TheSlowGrowth/TapeLooper/dsp/src/dsp/TapeLooper.h

/**
 * Copyright (C) Johannes Elliesen, 2021
 *
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
 * You should have received a copy of the GNU General Public License
 * along with this program. If not, see <http://www.gnu.org/licenses/>.
 */

#pragma once

#include "DspHelpers.h"
#include "Player.h"
#include "Recorder.h"
#include "TapeProcessor.h"
#include "WowAndFlutter.h"

#include "../util/Memory.h"

template <size_t numChannels_>
struct LooperStoragePtr
{
    float* data[numChannels_];
    size_t numSamples;
    static constexpr size_t numChannels = numChannels_;

    size_t getTotalSizeInBytes() const
    {
        return numChannels * numSamples * sizeof(float);
    }
};

struct MonoOrStereoLooperStoragePtr :
    public LooperStoragePtr<1>,
    public LooperStoragePtr<2>
{
};

template <size_t size, size_t numChannels>
class LooperStorage : public LooperStoragePtr<numChannels>
{
public:
    LooperStorage()
    {
        for (size_t ch = 0; ch < numChannels; ch++)
        {
            storage_[ch].fill(0.0f);
            this->data[ch] = storage_[ch].data();
        }
        this->numSamples = size;
    }

private:
    std::array<std::array<float, size>, numChannels> storage_;
};

template <size_t sizeWhenMono>
class MonoOrStereoLooperStorage : public MonoOrStereoLooperStoragePtr
{
public:
    MonoOrStereoLooperStorage()
    {
        storage_.fill(0.0f);

        this->LooperStoragePtr<1>::data[0] = storage_.data();
        this->LooperStoragePtr<1>::numSamples = sizeWhenMono;

        const auto sizePerChannel = sizeWhenMono / 2;
        this->LooperStoragePtr<2>::data[0] = storage_.data();
        this->LooperStoragePtr<2>::data[1] = storage_.data() + sizePerChannel;
        this->LooperStoragePtr<2>::numSamples = sizePerChannel;
    }

private:
    std::array<float, sizeWhenMono> storage_;
};

enum class LooperState
{
    stopped,
    playing,
    recording
};

template <size_t sampleRate, size_t numChannels>
class TapeLooper
{
public:
    using ProcessorType = TapeProcessor<sampleRate, numChannels>;
    using SpeedModulatorType = WowAndFlutterOscillator<float, sampleRate>;
    using PlayerType = Player<ProcessorType, SpeedModulatorType, sampleRate, numChannels>;
    using RecorderType = Recorder<sampleRate, numChannels>;

    TapeLooper(LooperStoragePtr<numChannels> storageToUse) :
        storage_(storageToUse),
        state_(LooperState::stopped),
        player_(AudioBufferPtr<numChannels, const float>(storage_.data, storage_.numSamples)),
        recorder_(AudioBufferPtr<numChannels, float>(storage_.data, storage_.numSamples))
    {
    }

    void switchState(LooperState newState)
    {
        switch (newState)
        {
            default:
            case LooperState::stopped:
                if (state_ == LooperState::recording)
                    recorder_.stopRecording();
                else if (state_ == LooperState::playing)
                    player_.stopPlaying();
                break;
            case LooperState::playing:
                if (preventPlayback_)
                    return;
                if (state_ == LooperState::recording)
                    recorder_.stopRecording();
                player_.startPlaying(recorder_.getCurrentRecordingLength());
                break;
            case LooperState::recording:
                if (preventRecording_)
                    return;
                if (state_ == LooperState::playing)
                    player_.stopPlaying();
                recorder_.startRecording();
                break;
        }
        state_ = newState;
    }

    bool isRecording() const { return recorder_.isRecording(); }

    LooperState getState() const { return state_; }

    void reset()
    {
        player_.reset();
        recorder_.reset();
    }

    void process(float paramSpeed,
                 float wowAndFlutterAmt,
                 Direction direction,
                 const typename ProcessorType::Parameters& processorParameters,
                 float paramPostGain,
                 AudioBufferPtr<numChannels, const float> input,
                 AudioBufferPtr<numChannels, float> outputToAddTo,
                 ExponentialSmoother::TimeConstant postGainSmootherTimeConstant =
                     ExponentialSmoother::TimeConstant(0.05f, sampleRate, 1),
                 ExponentialSmoother::TimeConstant speedSmootherTimeConstant =
                     ExponentialSmoother::TimeConstant(0.05f, sampleRate, 1))
    {
        const auto mappedWowAndFlutterAmt = wowAndFlutterAmt * wowAndFlutterAmt;
        player_.process(paramSpeed,
                        mappedWowAndFlutterAmt,
                        direction,
                        paramPostGain,
                        processorParameters,
                        outputToAddTo,
                        postGainSmootherTimeConstant,
                        speedSmootherTimeConstant);
        recorder_.process(input);

        const auto recordingStopped = state_ == LooperState::recording && !recorder_.isRecording();
        if (recordingStopped)
            switchState(LooperState::playing);
    }

    size_t getSaveAndRecallStorageSize() const
    {
        return recorder_.getSaveAndRecallStorageSize()
               + sizeof(uint8_t) // isPlaying?
               + storage_.getTotalSizeInBytes();
    }

    /**
     * Saves the state of the looper
     */
    template <typename StorageType>
    bool save(WritableMemory<StorageType>& mem) const
    {
        if (!recorder_.save(mem))
            return false;

        // write sample data
        for (size_t ch = 0; ch < numChannels; ch++)
        {
            if (!mem.writeRaw(storage_.data[ch], sizeof(float) * storage_.numSamples))
                return false;
        }

        const uint8_t isPlaying = state_ == LooperState::playing ? 1 : 0;

        return mem.writeItems(isPlaying);
    }

    /**
     * Stopps playback or recording and recalls the state of the looper, including
     *    - the length of the current recording
     *    - if the looper is currently playing
     *    - the sample data stored
     */
    template <typename StorageType>
    bool restore(ReadableMemory<StorageType>& mem)
    {
        if (preventRecording_)
            return false;
        if (!recorder_.restore(mem))
            return false;

        // read sample data
        for (size_t ch = 0; ch < numChannels; ch++)
        {
            if (!mem.readRaw(storage_.data[ch], sizeof(float) * storage_.numSamples))
                return false;
        }

        uint8_t isPlaying = 0;
        mem.readItems(isPlaying);

        switchState(isPlaying == 1 ? LooperState::playing : LooperState::stopped);
        return true;
    }

    void preventPlaybackAndRecording(bool stopRecordingImmediately = false)
    {
        preventPlayback_ = true;
        preventRecording_ = true;
        const auto previousState = getState();
        switchState(LooperState::stopped);
        if (previousState == LooperState::recording)
        {
            if (stopRecordingImmediately)
                recorder_.stopRecordingImmediately();
        }
    }

    void preventRecording(bool stopRecordingImmediately = false)
    {
        preventPlayback_ = false;
        preventRecording_ = true;

        if (getState() == LooperState::recording)
        {
            switchState(LooperState::stopped);
            if (stopRecordingImmediately)
                recorder_.stopRecordingImmediately();
        }
    }

    void liftRestrictions()
    {
        preventPlayback_ = false;
        preventRecording_ = false;
    }

    LooperStoragePtr<numChannels> getSampleStoragePtr() { return storage_; }
    void setPlaybackLength(size_t length) { recorder_.setCurrentPlaybackLength(length); }
    size_t getPlaybackLength() const { return recorder_.getCurrentRecordingLength(); }
    static constexpr size_t getNumChannels() { return numChannels; }
    static constexpr size_t getSampleRate() { return sampleRate; }

    RecorderType& recorderForTesting() { return recorder_; }

private:
    const LooperStoragePtr<numChannels> storage_;
    LooperState state_;
    PlayerType player_;
    RecorderType recorder_;
    bool preventPlayback_ = false;
    bool preventRecording_ = false;
};
