TheSlowGrowth/TapeLooper/dsp/src/dsp/DspHelpers.cpp

#include "DspHelpers.h"

/* original script taken from pichenettes/stmlib */
const float pitchRatioHigh[257] = {
    // clang-format off
    6.151958251e-04,  6.517772725e-04,  6.905339660e-04,  7.315952524e-04,
    7.750981699e-04,  8.211879055e-04,  8.700182794e-04,  9.217522585e-04,
    9.765625000e-04,  1.034631928e-03,  1.096154344e-03,  1.161335073e-03,
    1.230391650e-03,  1.303554545e-03,  1.381067932e-03,  1.463190505e-03,
    1.550196340e-03,  1.642375811e-03,  1.740036559e-03,  1.843504517e-03,
    1.953125000e-03,  2.069263856e-03,  2.192308688e-03,  2.322670146e-03,
    2.460783301e-03,  2.607109090e-03,  2.762135864e-03,  2.926381010e-03,
    3.100392680e-03,  3.284751622e-03,  3.480073118e-03,  3.687009034e-03,
    3.906250000e-03,  4.138527712e-03,  4.384617376e-03,  4.645340293e-03,
    4.921566601e-03,  5.214218180e-03,  5.524271728e-03,  5.852762019e-03,
    6.200785359e-03,  6.569503244e-03,  6.960146235e-03,  7.374018068e-03,
    7.812500000e-03,  8.277055425e-03,  8.769234752e-03,  9.290680586e-03,
    9.843133202e-03,  1.042843636e-02,  1.104854346e-02,  1.170552404e-02,
    1.240157072e-02,  1.313900649e-02,  1.392029247e-02,  1.474803614e-02,
    1.562500000e-02,  1.655411085e-02,  1.753846950e-02,  1.858136117e-02,
    1.968626640e-02,  2.085687272e-02,  2.209708691e-02,  2.341104808e-02,
    2.480314144e-02,  2.627801298e-02,  2.784058494e-02,  2.949607227e-02,
    3.125000000e-02,  3.310822170e-02,  3.507693901e-02,  3.716272234e-02,
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
    1.030231638e+00,  1.030464119e+00,  1.030696653e+00,  1.030929239e+00,
    1.031161878e+00,  1.031394569e+00,  1.031627313e+00,  1.031860109e+00,
    1.032092958e+00,  1.032325859e+00,  1.032558813e+00,  1.032791820e+00,
    1.033024879e+00,  1.033257991e+00,  1.033491155e+00,  1.033724372e+00,
    1.033957641e+00,  1.034190964e+00,  1.034424338e+00,  1.034657766e+00,
    1.034891246e+00,  1.035124779e+00,  1.035358364e+00,  1.035592003e+00,
    1.035825694e+00,  1.036059437e+00,  1.036293234e+00,  1.036527083e+00,
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
    // clang-format on
};
