TheSlowGrowth/TapeLooper/dsp/src/dsp/AudioBuffer.h

/**
 * Copyright (C) Johannes Elliesen, 2021
 *
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
 * You should have received a copy of the GNU General Public License
 * along with this program. If not, see <http://www.gnu.org/licenses/>.
 */

#pragma once

#include <array>

template <size_t numChannels, typename FloatType = float>
class AudioBufferPtr
{
public:
    AudioBufferPtr(FloatType* const* buffer, size_t numSamplesPerChannel) :
        size_(numSamplesPerChannel)
    {
        for (size_t ch = 0; ch < numChannels; ch++)
            buffer_[ch] = buffer[ch];
    }

    AudioBufferPtr(const AudioBufferPtr& other) = default;

    FloatType* operator[](size_t channelIdx)
    {
        return buffer_[channelIdx];
    }

    const FloatType* operator[](size_t channelIdx) const
    {
        return buffer_[channelIdx];
    }

    FloatType* const* getChannelPointers()
    {
        return buffer_;
    }

    const FloatType* const* getChannelPointers() const
    {
        return buffer_;
    }

    operator AudioBufferPtr<numChannels, const FloatType>() const
    {
        return AudioBufferPtr<numChannels, const FloatType>(buffer_, size_);
    }

    void fill(FloatType value)
    {
        for (size_t ch = 0; ch < numChannels; ch++)
            for (size_t i = 0; i < size_; i++)
                buffer_[ch][i] = value;
    }

    void copyToChannel(size_t destChannel, const FloatType* const srcSamples, size_t numSamples)
    {
        for (size_t i = 0; i < std::min(numSamples, size_); i++)
            buffer_[destChannel][i] = srcSamples[i];
    }

    void addToChannel(size_t destChannel, const FloatType* const srcSamples, size_t numSamples)
    {
        for (size_t i = 0; i < std::min(numSamples, size_); i++)
            buffer_[destChannel][i] += srcSamples[i];
    }

    void applyGain(FloatType value)
    {
        for (size_t ch = 0; ch < numChannels; ch++)
            for (size_t i = 0; i < size_; i++)
                buffer_[ch][i] *= value;
    }

    AudioBufferPtr<numChannels, FloatType> subBlock(size_t startSample, size_t length = size_t(-1)) const
    {
        const auto resultMaxLength = std::max(size_ - startSample, size_t(0));
        const auto resultLength = std::min(resultMaxLength, length);
        AudioBufferPtr<numChannels, FloatType> result(resultLength);
        for (size_t ch = 0; ch < numChannels; ch++)
            result.buffer_[ch] = buffer_[ch] + startSample;
        return result;
    }

    const size_t size_;

protected:
    // private ctor for use in subBlock()
    AudioBufferPtr(size_t numSamples) :
        size_(numSamples) {}

    FloatType* buffer_[numChannels];
};

template <size_t numChannels, size_t numSamples, typename FloatType = float>
class AudioBuffer : public AudioBufferPtr<numChannels, FloatType>
{
public:
    AudioBuffer() :
        AudioBufferPtr<numChannels, FloatType>(numSamples)
    {
        for (size_t ch = 0; ch < numChannels; ch++)
            this->buffer_[ch] = channelBuffers_[ch];
    }

private:
    std::array<FloatType[numSamples], numChannels> channelBuffers_;
};
