TheSlowGrowth/TapeLooper/firmware/src/ui/UiSettingsPage.h

/**
 * Copyright (C) Johannes Elliesen, 2021
 *
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
 * You should have received a copy of the GNU General Public License
 * along with this program. If not, see <http://www.gnu.org/licenses/>.
 */

#pragma once

#include <array>
#include <memory>

#include <ui/UI.h>
#include <dsp/TapeLooper.h>

#include "../constants.h"
#include "../LooperController.h"
#include "../hardware/UiHardwareTypes.h"
#include "LooperParameterProvider.h"

template <typename LooperControllerType, typename UiHardwareType, typename LooperParameterProviderType>
class UiSettingsPage : public daisy::UiPage
{
public:
    UiSettingsPage(LooperControllerType& looperController,
                   LooperParameterProviderType& looperParameterProvider,
                   daisy::UiPage& calibrationPage) :
        looperController_(looperController),
        looperParameterProvider_(looperParameterProvider),
        calibrationPage_(calibrationPage)
    {
    }

    virtual ~UiSettingsPage() {}

    bool IsOpaque(const daisy::UiCanvasDescriptor&) override { return false; }

    void Draw(const daisy::UiCanvasDescriptor& canvas) override
    {
        UiHardwareType& hardware = *((UiHardwareType*) canvas.handle_);

        // light up the settings page led
        if (currentSetting_ == Setting::direction)
            hardware.setLed(Led::settings, LedColour::pulsingRed);
        else if (currentSetting_ == Setting::numChannels)
            hardware.setLed(Led::settings, LedColour::pulsingYellow);
        else
            hardware.setLed(Led::settings, LedColour::pulsingGreen);

        // update channel octave LEDs to show the currently selected setting
        const auto updateChannelOctaveLeds = [&](size_t looperChannel, std::array<Led, 4> ledIds)
        {
            if (currentSetting_ == Setting::direction)
            {
                if (looperController_.getDirection(looperChannel) == Direction::forwards)
                {
                    hardware.setLed(ledIds[0], LedColour::off);
                    hardware.setLed(ledIds[1], LedColour::off);
                    hardware.setLed(ledIds[2], LedColour::red);
                    hardware.setLed(ledIds[3], LedColour::red);
                }
                else
                {
                    hardware.setLed(ledIds[0], LedColour::red);
                    hardware.setLed(ledIds[1], LedColour::red);
                    hardware.setLed(ledIds[2], LedColour::off);
                    hardware.setLed(ledIds[3], LedColour::off);
                }
            }
            else if (currentSetting_ == Setting::numChannels)
            {
                hardware.setLed(ledIds[0], LedColour::yellow);
                hardware.setLed(ledIds[1], LedColour::yellow);
                if (looperController_.getChannelLayout(looperChannel) == ChannelLayout::stereo)
                {
                    hardware.setLed(ledIds[2], LedColour::yellow);
                    hardware.setLed(ledIds[3], LedColour::yellow);
                }
                else
                {
                    hardware.setLed(ledIds[2], LedColour::off);
                    hardware.setLed(ledIds[3], LedColour::off);
                }
            }
            else
            {
                const auto acceleration = looperController_.getMotorAcceleration(looperChannel);
                hardware.setLed(ledIds[0],
                                acceleration == MotorAcceleration::verySlow
                                    ? LedColour::green
                                    : LedColour::off);
                hardware.setLed(ledIds[1],
                                (acceleration == MotorAcceleration::slow) || (acceleration == MotorAcceleration::medium)
                                    ? LedColour::green
                                    : LedColour::off);
                hardware.setLed(ledIds[2],
                                (acceleration == MotorAcceleration::medium) || (acceleration == MotorAcceleration::fast)
                                    ? LedColour::green
                                    : LedColour::off);
                hardware.setLed(ledIds[3],
                                acceleration == MotorAcceleration::veryFast
                                    ? LedColour::green
                                    : LedColour::off);
            }
        };
        updateChannelOctaveLeds(0, { Led::chA_m2, Led::chA_m1, Led::chA_p1, Led::chA_p2 });
        updateChannelOctaveLeds(1, { Led::chB_m2, Led::chB_m1, Led::chB_p1, Led::chB_p2 });
        updateChannelOctaveLeds(2, { Led::chC_m2, Led::chC_m1, Led::chC_p1, Led::chC_p2 });
        updateChannelOctaveLeds(3, { Led::chD_m2, Led::chD_m1, Led::chD_p1, Led::chD_p2 });
    }

    void OnFocusGained() override
    {
        currentSetting_ = Setting::direction;
        saveButtonState_ = false;
        loadButtonState_ = false;
    }

    bool OnButton(uint16_t buttonID, uint8_t numberOfPresses, bool isRetriggering) override
    {
        (void) (isRetriggering); // ignore this argument

        const Button button = Button(buttonID);

        trackLoadAndSaveButtonStates(button, numberOfPresses);

        // swallow but ignore button-up messages
        if (numberOfPresses < 1)
            return true;

        switch (button)
        {
            // channel up rocker switch
            case Button::chA_up:
                onUpButton(0);
                break;
            case Button::chB_up:
                onUpButton(1);
                break;
            case Button::chC_up:
                onUpButton(2);
                break;
            case Button::chD_up:
                onUpButton(3);
                break;
            // channel down rocker switch
            case Button::chA_down:
                onDownButton(0);
                break;
            case Button::chB_down:
                onDownButton(1);
                break;
            case Button::chC_down:
                onDownButton(2);
                break;
            case Button::chD_down:
                onDownButton(3);
                break;
            // cycle through settings; then return to base page
            case Button::settings:
                if (currentSetting_ == Setting::direction)
                    currentSetting_ = Setting::numChannels;
                else if (currentSetting_ == Setting::numChannels)
                    currentSetting_ = Setting::motorLag;
                else if (currentSetting_ == Setting::motorLag)
                    Close(); // close this page
                break;

            // open calibration menu when load and save pressed at the same time
            case Button::load:
            case Button::save:
                if (saveButtonState_ && loadButtonState_)
                {
                    auto* parent = GetParentUI();
                    Close();
                    parent->OpenPage(calibrationPage_);
                }
            default:
                break;
        }
        return true;
    }

    bool OnPotMoved(uint16_t, float) override
    {
        return false; // passthrough pot events to the base page
    }

private:
    UiSettingsPage(const UiSettingsPage&) = delete;
    UiSettingsPage& operator=(const UiSettingsPage&) = delete;

    void trackLoadAndSaveButtonStates(Button button, int numberOfPresses)
    {
        if (button == Button::save)
        {
            saveButtonState_ = numberOfPresses > 0;
        }
        if (button == Button::load)
        {
            loadButtonState_ = numberOfPresses > 0;
        }
    }

    void onUpButton(size_t looperChannel)
    {
        if (currentSetting_ == Setting::direction)
        {
            if (looperController_.getDirection(looperChannel) != Direction::forwards)
                looperController_.setDirection(looperChannel, Direction::forwards);
        }
        else if (currentSetting_ == Setting::numChannels)
        {
            if (looperController_.getChannelLayout(looperChannel) != ChannelLayout::stereo)
                looperController_.setChannelLayout(looperChannel, ChannelLayout::stereo);
        }
        else
        {
            auto currentAcceleration = looperController_.getMotorAcceleration(looperChannel);
            switch (currentAcceleration)
            {
                case MotorAcceleration::verySlow:
                    looperController_.setMotorAcceleration(looperChannel, MotorAcceleration::slow);
                    break;
                case MotorAcceleration::slow:
                    looperController_.setMotorAcceleration(looperChannel, MotorAcceleration::medium);
                    break;
                case MotorAcceleration::medium:
                    looperController_.setMotorAcceleration(looperChannel, MotorAcceleration::fast);
                    break;
                case MotorAcceleration::fast:
                    looperController_.setMotorAcceleration(looperChannel, MotorAcceleration::veryFast);
                    break;
                default:
                    break;
            }
        }
    }

    void onDownButton(size_t looperChannel)
    {
        if (currentSetting_ == Setting::direction)
        {
            if (looperController_.getDirection(looperChannel) != Direction::backwards)
                looperController_.setDirection(looperChannel, Direction::backwards);
        }
        else if (currentSetting_ == Setting::numChannels)
        {
            if (looperController_.getChannelLayout(looperChannel) != ChannelLayout::mono)
                looperController_.setChannelLayout(looperChannel, ChannelLayout::mono);
        }
        else
        {
            auto currentAcceleration = looperController_.getMotorAcceleration(looperChannel);
            switch (currentAcceleration)
            {
                case MotorAcceleration::veryFast:
                    looperController_.setMotorAcceleration(looperChannel, MotorAcceleration::fast);
                    break;
                case MotorAcceleration::fast:
                    looperController_.setMotorAcceleration(looperChannel, MotorAcceleration::medium);
                    break;
                case MotorAcceleration::medium:
                    looperController_.setMotorAcceleration(looperChannel, MotorAcceleration::slow);
                    break;
                case MotorAcceleration::slow:
                    looperController_.setMotorAcceleration(looperChannel, MotorAcceleration::verySlow);
                    break;
                default:
                    break;
            }
        }
    }

    enum class Setting
    {
        direction,
        numChannels,
        motorLag
    };
    Setting currentSetting_ = Setting::direction;

    bool saveButtonState_ = false;
    bool loadButtonState_ = false;

    LooperControllerType& looperController_;
    LooperParameterProviderType& looperParameterProvider_;

    daisy::UiPage& calibrationPage_;
};
