TheSlowGrowth/TapeLooper/firmware/src/ui/TapeLooperUi.h

/**
 * Copyright (C) Johannes Elliesen, 2021
 *
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
 * You should have received a copy of the GNU General Public License
 * along with this program. If not, see <http://www.gnu.org/licenses/>.
 */

#pragma once

#include <array>

#include <ui/UI.h>
#include <dsp/DspHelpers.h>

#include "LooperParameterProvider.h"
#include "UiBasePage.h"
#include "UiCalibrationPage.h"
#include "UiSettingsPage.h"
#include "UiLoadOrSavePage.h"
#include "UiRecordingPage.h"

template <typename UiHardwareType,
          typename PeakMeterType,
          typename LooperControllerType,
          typename ParameterProviderType,
          typename LoopLibraryType>
class TapeLooperUi
{
public:
    TapeLooperUi(UiHardwareType& uiHardware,
                 daisy::UiCanvasDescriptor::ClearFuncPtr clearFunction,
                 daisy::UiCanvasDescriptor::FlushFuncPtr flushFunction,
                 daisy::UiEventQueue& eventQueue,
                 const std::array<PeakMeterType, 4>& peakMeters,
                 LooperControllerType& looperController,
                 ParameterProviderType& looperParameterProvider,
                 LoopLibraryType& loopLibrary) :
        uiHardware_(uiHardware),
        eventQueue_(eventQueue),
        calibrationPage_(uiHardware),
        settingsPage_(looperController,
                      looperParameterProvider,
                      calibrationPage_),
        savePage_(looperController, loopLibrary),
        loadPage_(looperController, loopLibrary),
        recordingPage_(looperController),
        basePage_(peakMeters,
                  looperController,
                  looperParameterProvider,
                  settingsPage_,
                  savePage_,
                  loadPage_,
                  recordingPage_)
    {
        daisy::UiCanvasDescriptor ledCanvas;
        ledCanvas.clearFunction_ = clearFunction;
        ledCanvas.flushFunction_ = flushFunction;
        ledCanvas.handle_ = &uiHardware_;
        ledCanvas.id_ = 0;
        ledCanvas.updateRateMs_ = 20; // 50Hz

        ui_.Init(eventQueue_,
                 daisy::UI::SpecialControlIds {},
                 { ledCanvas });
        ui_.OpenPage(basePage_);
    }

    void process()
    {
        ui_.Process();
    }

private:
    TapeLooperUi(const TapeLooperUi&) = delete;
    TapeLooperUi& operator=(const TapeLooperUi&) = delete;

    UiHardwareType& uiHardware_;
    daisy::UiEventQueue& eventQueue_;
    daisy::UI ui_;
    UiCalibrationPage<UiHardwareType>
        calibrationPage_;
    UiSettingsPage<LooperControllerType,
                   UiHardwareType,
                   ParameterProviderType>
        settingsPage_;
    UiSavePage<LooperControllerType,
               UiHardwareType,
               LoopLibraryType>
        savePage_;
    UiLoadPage<LooperControllerType,
               UiHardwareType,
               LoopLibraryType>
        loadPage_;
    UiRecordingPage<LooperControllerType,
                    UiHardwareType>
        recordingPage_;
    UiBasePage<PeakMeterType,
               LooperControllerType,
               UiHardwareType,
               ParameterProviderType>
        basePage_;
};
